YevgeniYagudin/Pipelined-MIPS-VHDL/VHDL files/DMEMORY.VHD

						--  Dmemory module (implements the data
						--  memory for the MIPS computer)
LIBRARY IEEE;
USE IEEE.STD_LOGIC_1164.ALL;
USE IEEE.STD_LOGIC_ARITH.ALL;
USE IEEE.STD_LOGIC_SIGNED.ALL;

LIBRARY altera_mf;
USE altera_mf.altera_mf_components.all;

ENTITY dmemory IS
	PORT(	read_data 			: OUT 	STD_LOGIC_VECTOR( 31 DOWNTO 0 );
        	address 			: IN 	STD_LOGIC_VECTOR( 7 DOWNTO 0 );
        	write_data 			: IN 	STD_LOGIC_VECTOR( 31 DOWNTO 0 );
	   		MemRead, Memwrite 	: IN 	STD_LOGIC;
            clock,reset			: IN 	STD_LOGIC );
END dmemory;

ARCHITECTURE behavior OF dmemory IS
SIGNAL write_clock : STD_LOGIC;
BEGIN
	data_memory : altsyncram
	GENERIC MAP  (
		operation_mode => "SINGLE_PORT",
		width_a => 32,
		widthad_a => 8,
		lpm_type => "altsyncram",
		outdata_reg_a => "UNREGISTERED",
		init_file => "C:\TestPrograms\ModelSim\L1_Cache\asm_ver1\dmemory.hex",
		intended_device_family => "Cyclone"
	)
	PORT MAP (
		wren_a => memwrite,
		clock0 => write_clock,
		address_a => address,
		data_a => write_data,
		q_a => read_data	);
-- Load memory address register with write clock
		write_clock <= NOT clock;
		
		PROCESS
		begin
			WAIT UNTIL rising_edge(clock) AND Memwrite = '1';
			report "saved to mem: M["&to_string(conv_integer(address))&"]<="&to_string(conv_integer(write_data));
		end PROCESS;		
		
END behavior;
